josefalk/ESP32-C6-water-level-sensor/main/A02YYUW.h

#pragma once
#include <Arduino.h>
#include <HardwareSerial.h>

class A02YYUW {
public:
  A02YYUW(HardwareSerial &serial, int rxPin, int txPin);
  void begin(unsigned long baud);
  float getDistance();

private:
  HardwareSerial &serial;
  int rxPin, txPin;
};
